malte0811/Mathatron-docs/images/keyboard/switches.jpg

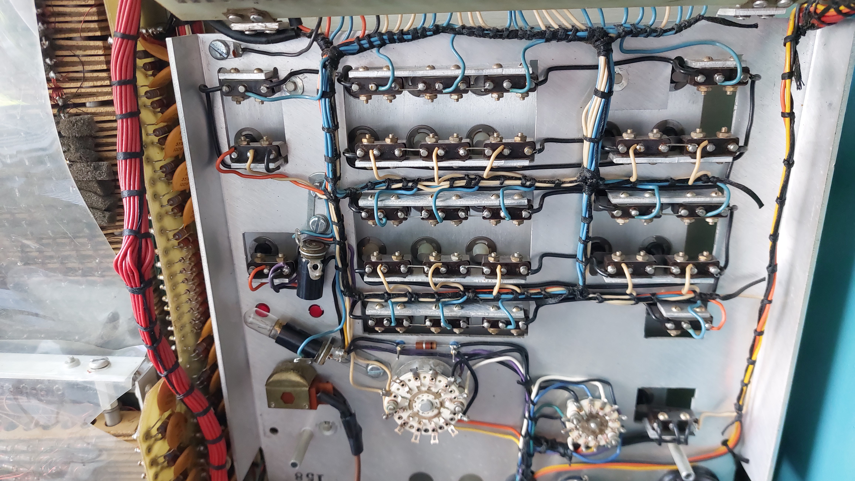
images/keyboard/switches.jpg
