malte0811/Mathatron-docs/schematics/keyboard.kicad_sch

## KiCad design schematics/keyboard.kicad_sch (2025-05-25)

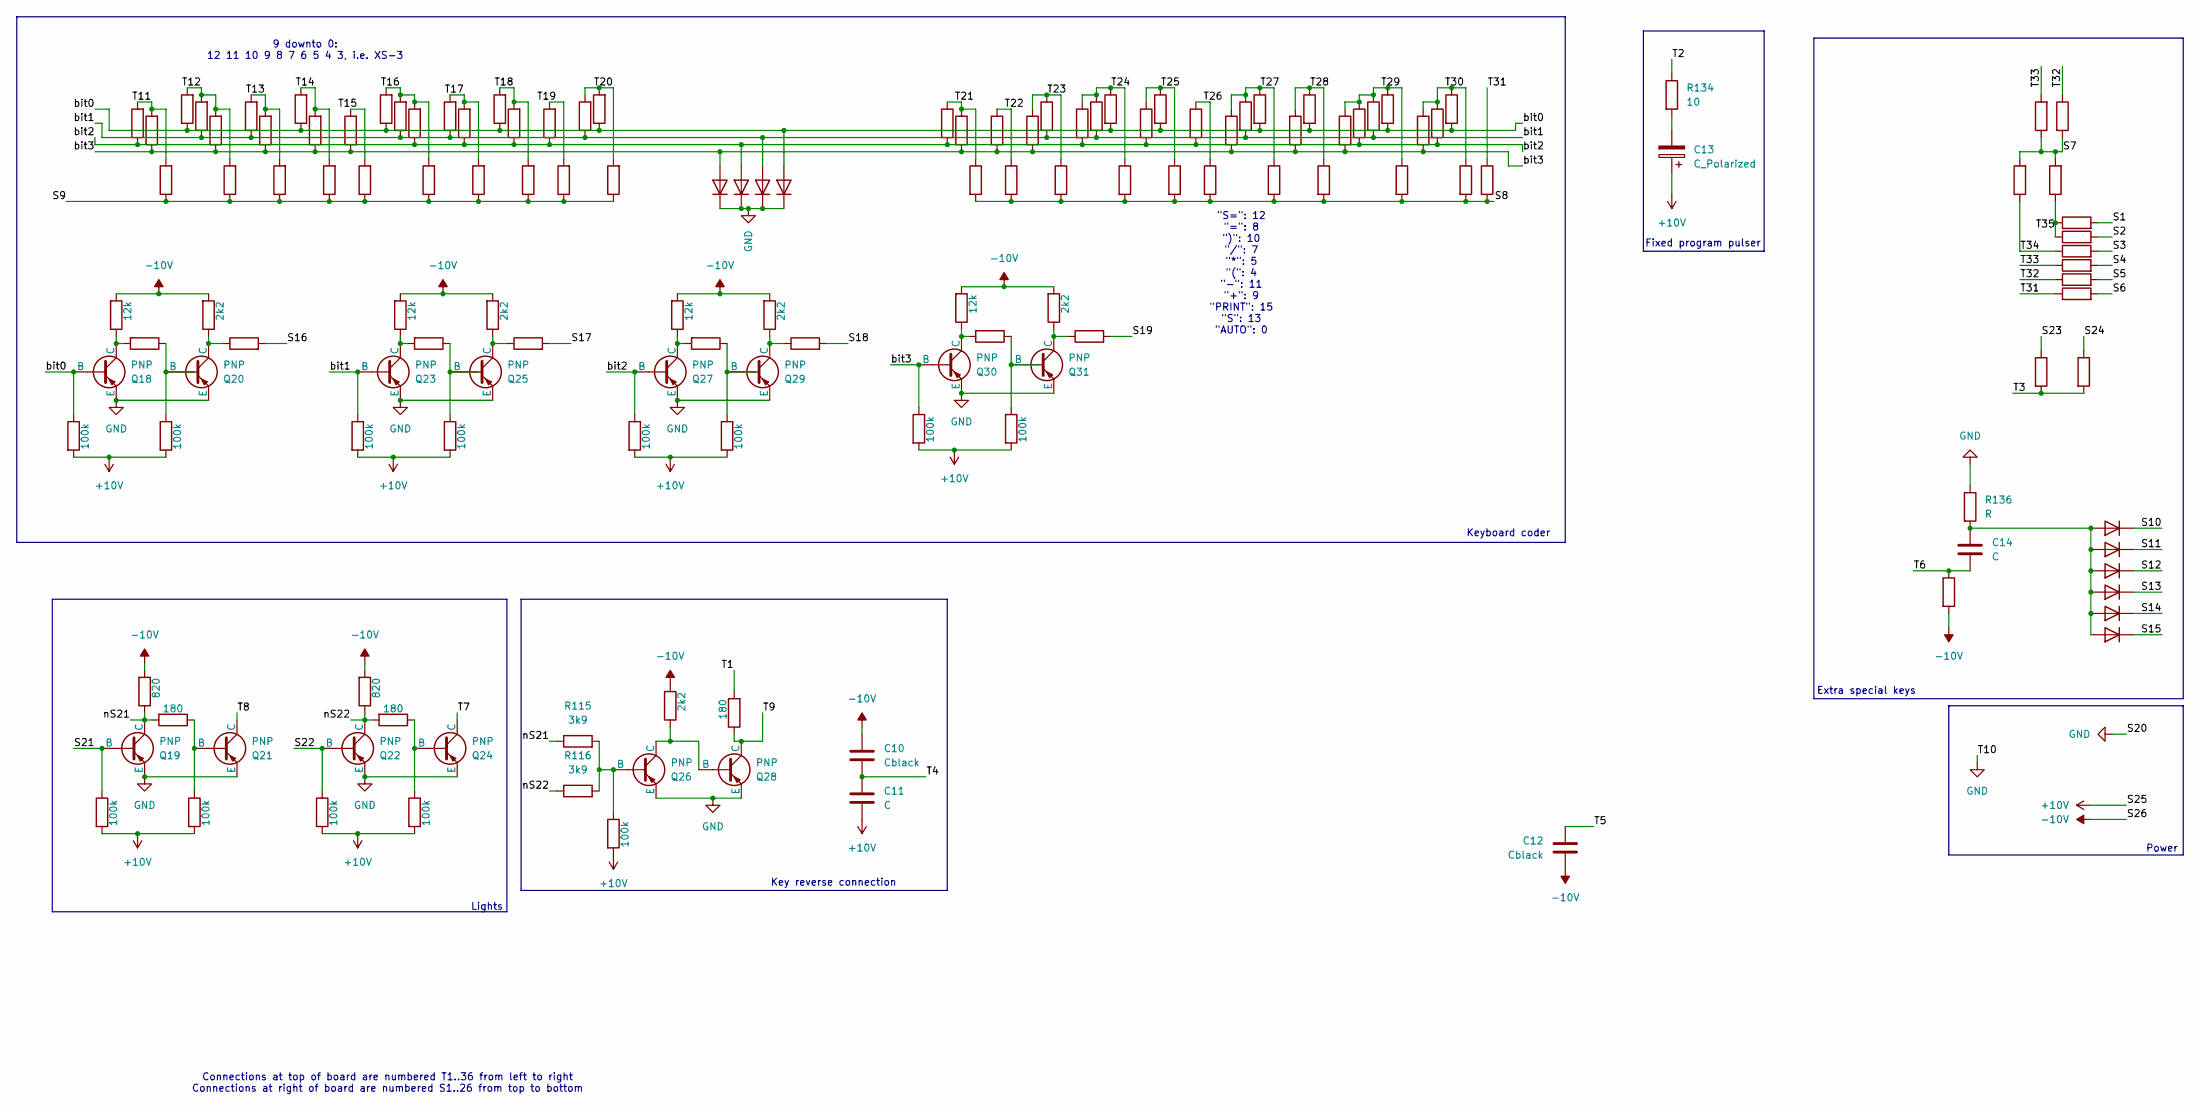
[picture p24: schematic keyboard.kicad_sch]

Parts:
C10, C12: Cblack
C11, C14: C
C13: C_Polarized
D7, D8, D9, D10, D11, D12, D13, D14, D15, D16: D
Q18, Q19, Q20, Q21, Q22, Q23, Q24, Q25, Q26, Q27, Q28, Q29, Q30, Q31: PNP
R25, R26, R27, R36, R37, R38, R39, R40, R41, R42, R43, R44, R45, R46, R47, R48, R49, R50, R51, R52, R53, R54, R55, R56, R57, R58, R59, R60, R61, R62, R63, R64, R65, R69, R70, R72, R82, R85, R91, R94, R96, R97, R98, R99, R100, R101, R102, R103, R104, R105, R106, R107, R108, R109, R110, R111, R112, R113, R114, R129, R130, R131, R132, R133, R135, R137, R138, R139, R140, R141, R142, R143, R144, R145, R146, R147, R148: 27k
R66, R67, R71, R74, R80, R83, R84, R86, R90, R117, R120, R123, R126: 100k
R68, R79, R118, R124: 12k
R73, R78, R81, R93, R119, R122, R125, R128, R136: R
R75, R87: 820
R76, R89, R95: 180
R77, R88, R92, R121, R127: 2k2
R115, R116: 3k9
R134: 10

Connections:
+10V: C11.2, C13.1, R66.2, R67.2, R71.2, R74.2, R80.2, R83.2, R84.2, R86.2, R90.2, R117.2, R120.2, R123.2, R126.2
-10V: C10.1, C12.2, R68.2, R75.2, R77.2, R79.2, R87.2, R88.2, R92.2, R118.2, R121.2, R124.2, R127.2, R135.2
GND: D7.1 (K), D8.1 (K), D9.1 (K), D10.1 (K), Q18.3 (E), Q19.3 (E), Q20.3 (E), Q21.3 (E), Q22.3 (E), Q23.3 (E), Q24.3 (E), Q25.3 (E), Q26.3 (E), Q27.3 (E), Q28.3 (E), Q29.3 (E), Q30.3 (E), Q31.3 (E), R136.1
unnamed: C13.2, R134.2
unnamed: C14.1, D11.2 (A), D12.2 (A), D13.2 (A), D14.2 (A), D15.2 (A), D16.2 (A), R136.2
unnamed: Q18.1 (C), R68.1, R73.2
unnamed: Q20.1 (C), R77.1, R78.1
unnamed: Q20.2 (B), R73.1, R74.1
unnamed: Q21.2 (B), R76.1, R80.1
unnamed: Q23.1 (C), R124.1, R125.2
unnamed: Q24.2 (B), R89.1, R90.1
unnamed: Q25.1 (C), R127.1, R128.1
unnamed: Q25.2 (B), R125.1, R126.1
unnamed: Q26.1 (C), Q28.2 (B), R92.1
unnamed: Q26.2 (B), R83.1, R115.2, R116.2
unnamed: Q27.1 (C), R118.1, R119.2
unnamed: Q29.1 (C), R121.1, R122.1
unnamed: Q29.2 (B), R119.1, R120.1
unnamed: Q30.1 (C), R79.1, R81.2
unnamed: Q31.1 (C), R88.1, R93.1
unnamed: Q31.2 (B), R81.1, R86.1
S1: R142.2
S2: R143.2
S3: R144.2
S4: R145.2
S5: R146.2
S6: R147.2
S7: R137.2, R138.1, R140.2, R141.2
S8: R25.2, R72.2, R85.2, R97.2, R100.2, R102.2, R106.2, R109.2, R114.2, R132.2, R133.2
S9: R36.1, R38.1, R41.1, R45.1, R48.1, R50.1, R54.1, R57.1, R60.1, R65.1
S10: D11.1 (K)
S11: D12.1 (K)
S12: D13.1 (K)
S13: D14.1 (K)
S14: D15.1 (K)
S15: D16.1 (K)
S16: R78.2
S17: R128.2
S18: R122.2
S19: R93.2
S21: Q19.2 (B), R67.1
S22: Q22.2 (B), R84.1
S23: R139.1
S24: R148.1
T1: R95.2
T2: R134.1
T3: R139.2, R148.2
T4: C10.2, C11.1
T5: C12.1
T6: C14.2, R135.1
T7: Q24.1 (C)
T8: Q21.1 (C)
T9: Q28.1 (C), R95.1
T11: R60.2, R61.2, R62.2
T12: R56.2, R57.2, R58.2, R59.2
T13: R53.2, R54.2, R55.2
T14: R50.2, R51.2, R52.2
T15: R48.2, R49.2
T16: R44.2, R45.2, R46.2, R47.2
T17: R41.2, R42.2, R43.2
T18: R38.2, R39.2, R40.2
T19: R36.2, R37.2
T20: R63.2, R64.2, R65.2
T21: R69.1, R70.1, R72.1
T22: R82.1, R85.1
T23: R25.1, R26.1, R27.1
T24: R91.1, R94.1, R96.1, R97.1
T25: R98.1, R99.1, R100.1
T26: R101.1, R102.1
T27: R103.1, R104.1, R105.1, R106.1
T28: R107.1, R108.1, R109.1
T29: R110.1, R111.1, R112.1, R113.1, R114.1
T30: R129.1, R130.1, R131.1, R132.1
T31: R133.1, R147.1
T32: R141.1, R146.1
T33: R138.2, R145.1
T34: R137.1, R144.1
T35: R140.1, R142.1, R143.1
bit0: D10.2 (A), Q18.2 (B), R40.1, R47.1, R52.1, R59.1, R64.1, R66.1, R96.2, R99.2, R105.2, R108.2, R113.2, R131.2
bit1: D9.2 (A), Q23.2 (B), R26.2, R43.1, R46.1, R55.1, R58.1, R63.1, R94.2, R104.2, R112.2, R123.1
bit2: D8.2 (A), Q27.2 (B), R37.1, R39.1, R42.1, R44.1, R62.1, R69.2, R91.2, R98.2, R101.2, R111.2, R117.1, R130.2
bit3: D7.2 (A), Q30.2 (B), R27.2, R49.1, R51.1, R53.1, R56.1, R61.1, R70.2, R71.1, R82.2, R103.2, R107.2, R110.2, R129.2
nS21: Q19.1 (C), R75.1, R76.2, R115.1
nS22: Q22.1 (C), R87.1, R89.2, R116.1

Notes on the sheet:
Power
Fixed program pulser
Connections at top of board are numbered T1..36 from left to right Connections at right of board are numbered S1..26 from top to bottom
9 downto 0: 12 11 10 9 8 7 6 5 4 3, i.e. XS-3
Lights
Keyboard coder
Extra special keys
Key reverse connection
"S=": 12 "=": 8 ")": 10 "/": 7 "*": 5 "(": 4 "-": 11 "+": 9 "PRINT": 15 "S": 13 "AUTO": 0
