malte0811/Mathatron-docs/schematics/mixed.kicad_sch

## KiCad design schematics/mixed.kicad_sch (2025-05-25)

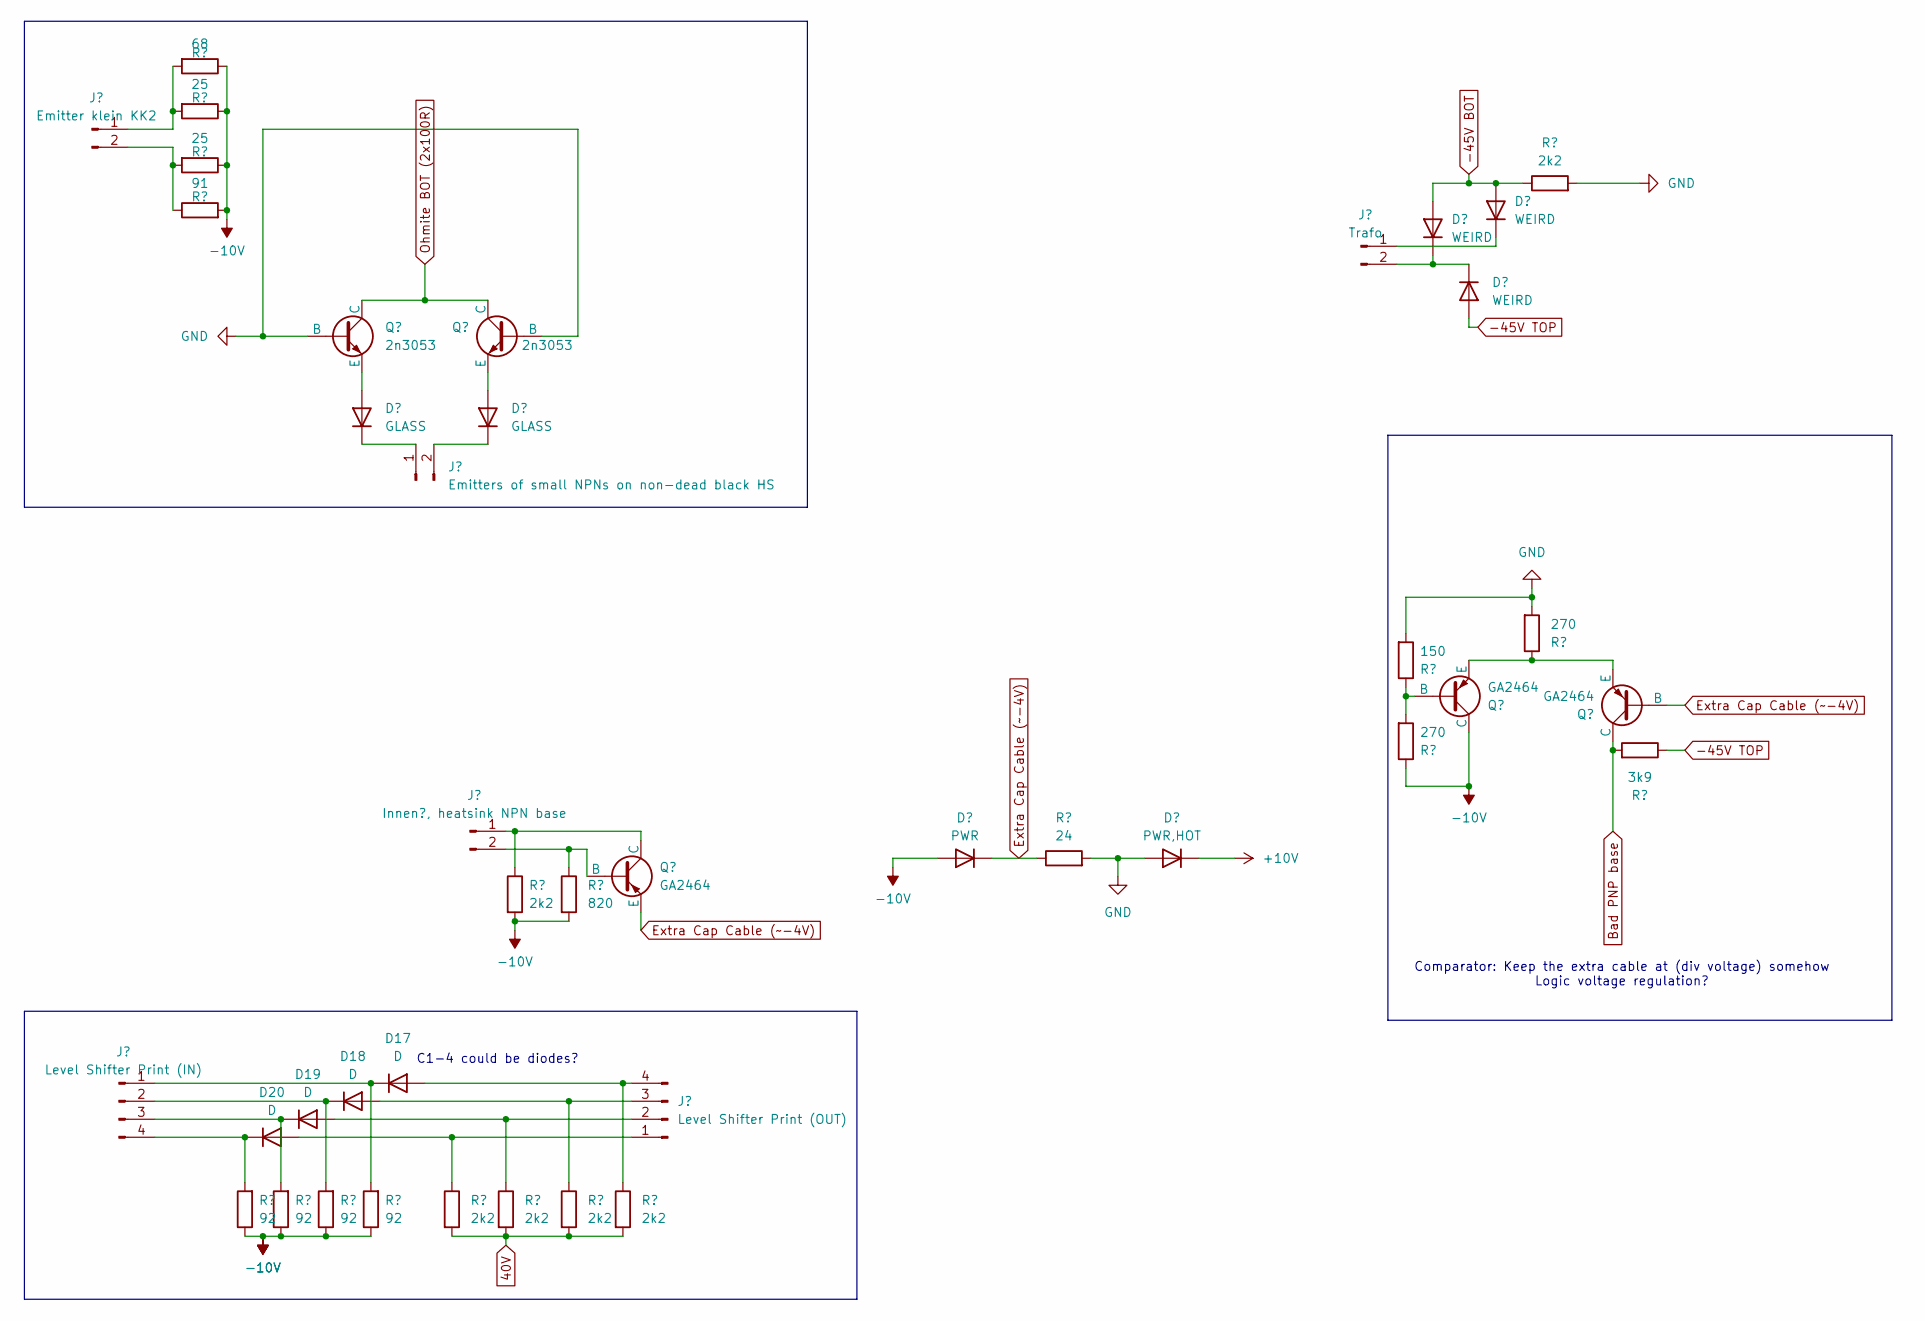
[picture p26: schematic mixed.kicad_sch]

Parts:
D1: PWR
D2: PWR,HOT
D3, D4: GLASS
D5, D6, D7: WEIRD
D17, D18, D19, D20: D
J1: Level Shifter Print (IN)
J2: Level Shifter Print (OUT)
J3: Emitter klein KK2
J4: Innen?, heatsink NPN base
J6: Emitters of small NPNs on non-dead black HS
J7: Trafo
Q1, Q4, Q5: GA2464
Q2, Q3: 2n3053
R1, R2, R3, R4: 92
R5, R6, R7, R8, R13, R16: 2k2
R9, R10: 25
R11: 68
R12: 91
R14: 820
R15: 24
R17: 3k9
R18, R19: 270
R20: 150

Connections:
40V: R5.2, R6.2, R7.2, R8.2
+10V: D2.1 (K)
-10V: D1.2 (A), Q4.1 (C), R1.1, R2.1, R3.1, R4.1, R9.1, R10.1, R11.1, R12.2, R13.2, R14.2, R19.1
-45V BOT: D5.2 (A), D6.2 (A), R16.1
-45V TOP: D7.2 (A), R17.1
Bad PNP base: Q5.1 (C), R17.2
Extra Cap Cable (~-4V): D1.1 (K), Q1.3 (E), Q5.2 (B), R15.1
GND: D2.2 (A), Q2.2 (B), Q3.2 (B), R15.2, R16.2, R18.2, R20.2
unnamed: D3.1 (K), J6.1
unnamed: D3.2 (A), Q2.3 (E)
unnamed: D4.1 (K), J6.2
unnamed: D4.2 (A), Q3.3 (E)
unnamed: D5.1 (K), D7.1 (K), J7.2
unnamed: D6.1 (K), J7.1
unnamed: D17.1 (K), J1.1, R4.2
unnamed: D17.2 (A), J2.4, R8.1
unnamed: D18.1 (K), J1.2, R3.2
unnamed: D18.2 (A), J2.3, R7.1
unnamed: D19.1 (K), J1.3, R2.2
unnamed: D19.2 (A), J2.2, R6.1
unnamed: D20.1 (K), J1.4, R1.2
unnamed: D20.2 (A), J2.1, R5.1
unnamed: J3.1, R9.2, R11.2
unnamed: J3.2, R10.2, R12.1
unnamed: J4.1, Q1.1 (C), R13.1
unnamed: J4.2, Q1.2 (B), R14.1
unnamed: Q4.2 (B), R19.2, R20.1
unnamed: Q4.3 (E), Q5.3 (E), R18.1
Ohmite BOT (2x100R): Q2.1 (C), Q3.1 (C)

Notes on the sheet:
Comparator: Keep the extra cable at (div voltage) somehow Logic voltage regulation?
C1-4 could be diodes?
