malte0811/Mathatron-docs/schematics/printer.kicad_sch

## KiCad design schematics/printer.kicad_sch (2025-05-25)

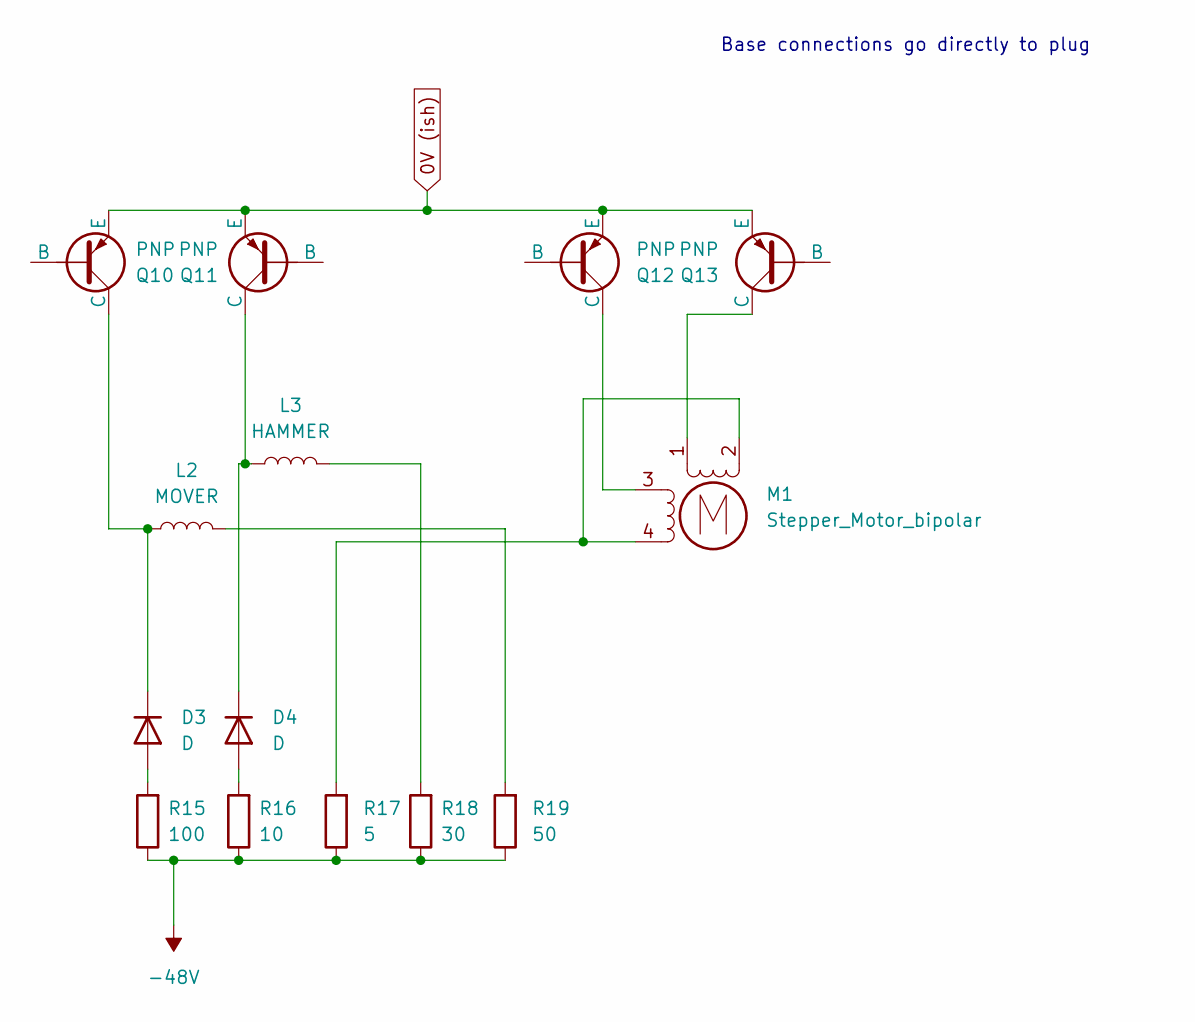
[picture p27: schematic printer.kicad_sch]

Parts:
D3, D4: D
L2: MOVER
L3: HAMMER
M1: Stepper_Motor_bipolar
Q10, Q11, Q12, Q13: PNP
R15: 100
R16: 10
R17: 5
R18: 30
R19: 50

Connections:
0V (ish): Q10.3 (E), Q11.3 (E), Q12.3 (E), Q13.3 (E)
-48V: R15.1, R16.1, R17.1, R18.1, R19.1
unnamed: D3.1 (K), L2.1, Q10.1 (C)
unnamed: D3.2 (A), R15.2
unnamed: D4.1 (K), L3.1, Q11.1 (C)
unnamed: D4.2 (A), R16.2
unnamed: L2.2, R19.2
unnamed: L3.2, R18.2
unnamed: M1.1, Q13.1 (C)
unnamed: M1.2 (-), M1.4, R17.2
unnamed: M1.3, Q12.1 (C)

Notes on the sheet:
Base connections go directly to plug
